CodeChix-OpenSource/PiDoorbell/wiring/led-always-on.jpg

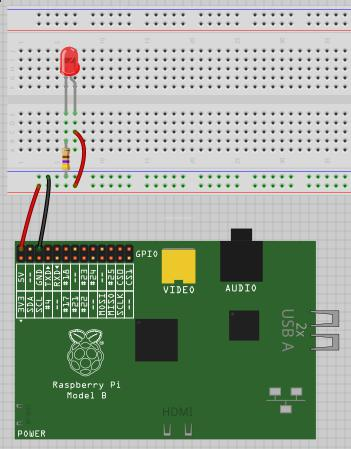
wiring/led-always-on.jpg
