CodeChix-OpenSource/PiDoorbell/piphoto.py

#!/usr/bin/env python

# Copyright (C) 2014 Akkana Peck <akkana@shallowsky.com>
#
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
#
# Take a still photo. If a USB camera is attached (/dev/video0), use it,
# else if a PiCam is attached (/dev/fb0), use that instead,
# else throw an exception.
#

import os
from subprocess import call
import time

def take_still(outfile='/tmp/still.jpg', res=[640, 480], verbose=False):

    # Do we have a USB camera for which we can use fswebcam?
    if os.path.exists('/dev/video0'):
        if verbose:
            print "Taking photo with fswebcam ..."

        rv = call(['/usr/bin/fswebcam', '-d', '/dev/video0',
                              '-r', '%dx%d' % tuple(res), outfile])

        if not rv:
            return

        print "fswebcam failed! Error code %d" % rv

    # No luck with a USB camera. Is there a Pi camera?
    if not os.path.exists('/dev/fb0'):
        raise SystemError, "Can't find either a USB camera or a Pi camera!"

    # Can we use the picamera module?
    try:
        import picamera
    except ImportError:
        # picamera isn't installed. Can we use raspistill?
        if not os.path.exists('/usr/bin/raspistill'):
            raise SystemError, \
                "Neither python-picamera nor raspistill is installed"
        if verbose:
            print "Taking photo with raspistill"
        rv = call(['/usr/bin/raspistill', '-o', outfile])
        if rv:
            raise "raspistill exited with %d" % rv
        return

    if verbose:
        print "Taking photo with picamera"
    with picamera.PiCamera() as camera:
        camera.resolution = res
        camera.start_preview()
        # Camera warm-up time
        time.sleep(2)
        camera.capture(outfile)

        # Is this needed? What does previewing mean?
        camera.stop_preview()

if __name__ == '__main__':
    take_photo(verbose=True)
