CodeChix-OpenSource/PiDoorbell/send_notifications.py

#!/usr/bin/env python

# Copyright (C) 2013-2014 Rupa Dachere <rupa@codechix.org>>
#
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

# Download the twilio-python library from http://twilio.com/docs/libraries
# Use python-twitter to tweet - github.com/bear/python-twitter

import sys
sys.path.append("/home/pi/pycon2013/pidoorbell")
from twilio.rest import TwilioRestClient
import twitter
import optparse
import sms_auth_info
 
def send_sms(sms_url):

        client = TwilioRestClient(sms_auth_info.account_sid, sms_auth_info.auth_token)
 
        print '\n\n ************************ SENDING SMS WITH URL: ', sms_url ," *************************\n\n"

        body_url = "PiDoorbell for PyCon 2014! Visitor @FrontDoor: " + sms_url

	## to: you cell phone number;  from: twilio's assigned number (from "numbers" tab on your acct.)
        message = client.sms.messages.create(to="+1XXXYYYZZZZ", from_="+1XXXYYYZZZZ", body=body_url)

def send_tweet(tweet_url):

        api = twitter.Api(consumer_key=sms_auth_info.twitter_auth_key, consumer_secret=sms_auth_info.twitter_auth_secret, \
		access_token_key=sms_auth_info.twitter_access_key, access_token_secret=sms_auth_info.twitter_access_secret)

        api.VerifyCredentials()

        print '\n\n ************************ SENDING TWEET WITH URL: ', tweet_url ," *************************\n\n"

        post_message = "PiDoorbell for #pycon2014 using GPIO!! Visitor @FrontDoor: " + tweet_url
        status = api.PostUpdate(post_message)
        #print status


#### MAIN ####

parser = optparse.OptionParser()

parser.add_option('-u', '--sms_url',
    action="store", dest="sms_url",
    help="sms url string", default="spam")

parser.add_option('-m', '--mode',
    action="store", dest="mode",
    help="mode: \"sms\" or \"tweet\" or \"all\"", default="spam")

options, args = parser.parse_args()

if options.sms_url == "spam" or options.mode == "spam":
  print "**** HEY! You forgot the URL or MODE for the SMS: ***"
  print "**** Usage: send_sms -m <sms/tweet/all> -u <URL_string> ***"
  sys.exit()


if options.mode == "sms":
    send_sms(options.sms_url)
elif options.mode == "tweet":
    send_tweet(options.sms_url)
else:
    send_sms(options.sms_url)
    send_tweet(options.sms_url)
